Deliciozy/HWSW1/schematics/Wearable.kicad_sch

## KiCad design schematics/Wearable.kicad_sch (2026-01-26)

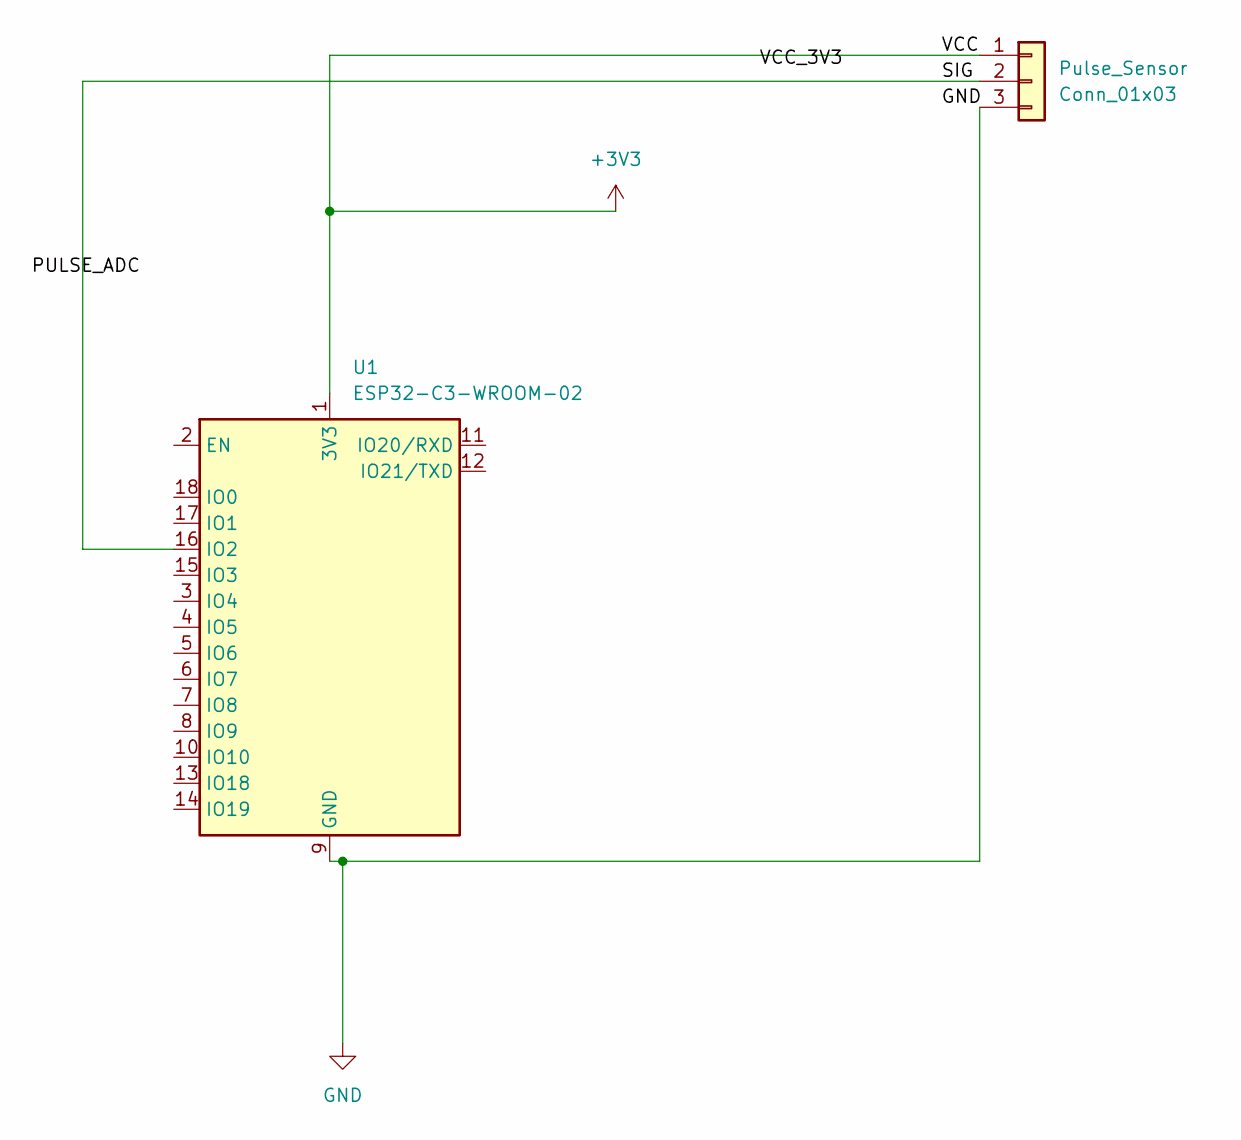
[picture p5: schematic Wearable.kicad_sch]

Parts:
Pulse_Sensor: Conn_01x03
U1: ESP32-C3-WROOM-02

Connections:
+3V3: Pulse_Sensor.1, U1.1 (3V3)
GND: Pulse_Sensor.3, U1.9 (GND), U1.19 (GND)
SIG: Pulse_Sensor.2, U1.16 (IO2)
