Deliciozy/HWSW1/schematics/device.kicad_sch

## KiCad design schematics/device.kicad_sch (2026-01-26)

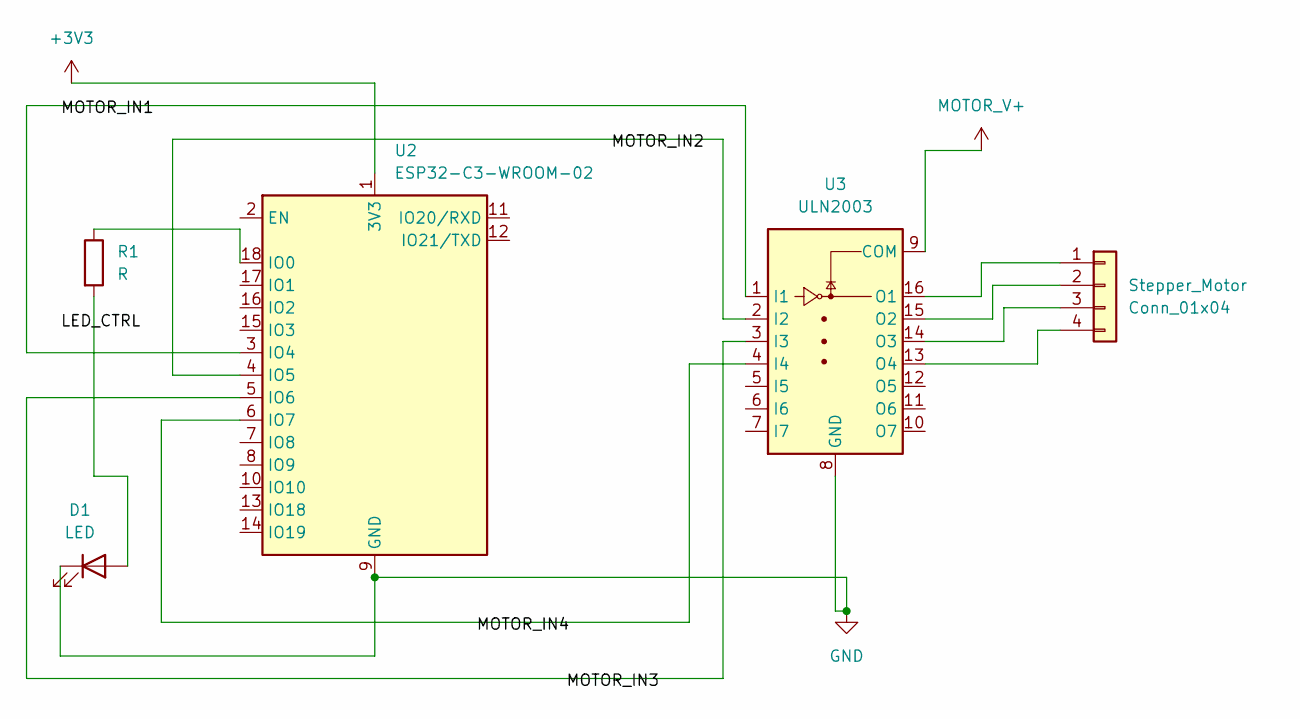
[picture p6: schematic device.kicad_sch]

Parts:
D1: LED
R1: R
Stepper_Motor: Conn_01x04
U2: ESP32-C3-WROOM-02
U3: ULN2003

Connections:
+3V3: U2.1 (3V3)
GND: D1.1 (K), U2.9 (GND), U2.19 (GND), U3.8 (GND)
MOTOR_V+: U3.9 (COM)
unnamed: D1.2 (A), R1.2
unnamed: R1.1, U2.18 (IO0)
unnamed: Stepper_Motor.1, U3.16 (O1)
unnamed: Stepper_Motor.2, U3.15 (O2)
unnamed: Stepper_Motor.3, U3.14 (O3)
unnamed: Stepper_Motor.4, U3.13 (O4)
unnamed: U2.3 (IO4), U3.1 (I1)
unnamed: U2.4 (IO5), U3.2 (I2)
unnamed: U2.5 (IO6), U3.3 (I3)
unnamed: U2.6 (IO7), U3.4 (I4)
